glowingkitty/The-Glowing-Stripes-Project/src/webserver.cpp

#include <Arduino.h>

#include <AsyncTCP.h>
#include <ESPAsyncWebServer.h>

AsyncWebServer server(80);

const char* PARAM_MESSAGE = "Hello world";

void notFound(AsyncWebServerRequest *request) {
    request->send(404, "text/plain", "Not found");
}

void start_server(){
    server.on("/", HTTP_GET, [](AsyncWebServerRequest *request){
        request->send(200, "text/plain", "Hello, world");
    });

    // Send a GET request to <IP>/get?message=<message>
    server.on("/get", HTTP_GET, [] (AsyncWebServerRequest *request) {
        String message;
        if (request->hasParam(PARAM_MESSAGE)) {
            message = request->getParam(PARAM_MESSAGE)->value();
        } else {
            message = "No message sent";
        }
        request->send(200, "text/plain", "Hello, GET: " + message);
    });

    // Send a POST request to <IP>/post with a form field message set to <message>
    server.on("/post", HTTP_POST, [](AsyncWebServerRequest *request){
        String message;
        if (request->hasParam(PARAM_MESSAGE, true)) {
            message = request->getParam(PARAM_MESSAGE, true)->value();
        } else {
            message = "No message sent";
        }
        request->send(200, "text/plain", "Hello, POST: " + message);
    });

    server.onNotFound(notFound);

    server.begin();
}
