glowingkitty/The-Glowing-Stripes-Project/www/host.py

import os
import socket
import sys
import time
from time import sleep

from MicroWebSrv2 import *

import network
import webrepl
from machine import Pin


class Host():
    def __init__(self,
                 host_wifi_name='🌟GlowingStripes',
                 host_wifi_password='letsglow',
                 webrepl_password='letsglow',
                 dreamcolor_input_pin_num=5,
                 test=False
                 ):
        # Wlan
        self.host_wifi_name = host_wifi_name
        self.host_wifi_password = host_wifi_password
        self.webrepl_password = webrepl_password
        self.wlan = None
        self.ap = None

        # setting up the LEDs
        self.test = test
        self.dreamcolor_input_pin_num = dreamcolor_input_pin_num
        self.dreamcolor_input_pin = Pin(self.dreamcolor_input_pin_num, Pin.IN)

        # setting up server
        self.default_mode = 'glow_rainbow'

    def activate_wifi(self):
        if self.test:
            print('Wifi can only be used on real hardware, not in test mode.')
        else:
            print('Activate WiFi...')
            self.wlan = network.WLAN(network.STA_IF)
            self.wlan.active(True)

    def scan_wifis(self):
        if self.test:
            print('Wifi can only be used on real hardware, not in test mode.')
        else:
            print('Scan for nearby WiFi networks...')
            if not self.wlan:
                self.activate_wifi()

            return self.wlan.scan()

    def start_host_wifi(self):
        if self.test:
            print('Wifi can only be used on real hardware, not in test mode.')
        else:
            print('Starting host wifi...')
            self.ap = network.WLAN(network.AP_IF)
            self.ap.active(True)
            self.ap.config(essid=self.host_wifi_name,
                           authmode=network.AUTH_WPA_WPA2_PSK,
                           password=self.host_wifi_password)
            print('Host wifi accessible now as "{}"'.format(self.host_wifi_name))

    def activate_webrepl(self):
        if self.test:
            print('webrepl can only be used on real hardware, not in test mode.')
        else:
            print('Activate webrepl...')
            if not self.ap:
                print('Host wifi not active yet. Start host wifi...')
                self.start_host_wifi()
            webrepl.start(password=self.webrepl_password)

    def start_server(self):
        print('Starting server...')

        @WebRoute(GET, '/mode', name='Current mode')
        def RequestMode(microWebSrv2, request):
            request.Response.ReturnOkJSON({
                'current_mode': 'glow_rainbow'
            })

        @WebRoute(GET, '/files', name='Overview of available files')
        def RequestFiles(microWebSrv2, request):
            request.Response.ReturnOkJSON({
                'files': ['stripe.py']
            })

        mws2 = MicroWebSrv2()
        mws2.SetEmbeddedConfig()
        mws2._slotsCount = 4
        mws2.StartManaged()

        # Main program loop until keyboard interrupt,
        try:
            while True:
                sleep(1)
        except KeyboardInterrupt:
            mws2.Stop()

    def on(self):
        self.start_host_wifi()
        self.start_server()

    def restart(self):
        if self.test:
            print('Restart can only be performed on real hardware, not in test mode.')
        else:
            import machine
            machine.reset()
